juarendra/Zeapad-QMK-VIA/FIRMWARE/zeapadstm32_artsey/keymaps/default/keymap.c

/* Copyright 2024 Juarendra Ramadhani <jrjuarendra@gmail.com>
 *
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
 * You should have received a copy of the GNU General Public License
 * along with this program.  If not, see <http://www.gnu.org/licenses/>.
*/
#include QMK_KEYBOARD_H
#include "midi.h"
//#include "encoder.c"

extern MidiDevice midi_device;


enum layers {
  _ART_BASE,
  _ART_NUM,
  _ART_CUS,
  _ART_PUNC,
  _ART_MOU,
  _ART_NAV,
  _ART_SYM,
};

#include "aliases.c"
#include "combos.c"

#define LAYOUT_via( \
    k00, k01, k02, k03, \
    k10, k11, k12, k13,\
    k20, k21, k22, k23,\
    k30, k31, k32, k33\
) \
{ \
    { k00, k01, k02, k03}, \
    { k10, k11, k12, k13}, \
    { k20, k21, k22, k23}, \
    { k30, k31, k32, k33} \
}

enum midi_cc_keycodes_LTRM { MIDI_CC1 = QK_USER_0, MIDI_CC2, MIDI_CC3, MIDI_CC4, MIDI_CC5, MIDI_CC6, MIDI_CC7, MIDI_CC8, MIDI_CC9, MIDI_CC10, MIDI_CC11, MIDI_CC12, MIDI_CC13, MIDI_CC14, MIDI_CC15, MIDI_ENCH1_1, MIDI_ENCH1_2, MIDI_ENCH2_1, MIDI_ENCH2_2, MIDI_ENCH3_1, MIDI_ENCH3_2};
static uint8_t current_MIDI_ccNumber         = 1;
static uint8_t current_MIDI_ccNumber1        = 16;
static uint8_t current_MIDI_ccNumber2        = 31;


const uint16_t PROGMEM keymaps[][MATRIX_ROWS][MATRIX_COLS] = {

[_ART_BASE] = LAYOUT_via(
    KC_P7,    LCTL(LSFT(KC_E)),             KC_ENTER,                TO(1),    
    KC_P4,    LCTL(KC_C),                   LCTL(KC_V),              KC_ESC,      
	BASE_1_1,		BASE_1_2,		BASE_1_3,		BASE_1_4,
	BASE_2_1,		BASE_2_2,		BASE_2_3,		BASE_2_4
),

[_ART_NUM] = LAYOUT_via(
    KC_TRNS,   KC_TRNS,   KC_TRNS,    TO(2),
    KC_TRNS,   KC_TRNS,   KC_TRNS,    KC_TRNS,
	NUM_1_1,		NUM_1_2,		NUM_1_3,		NUM_1_4,
	NUM_2_1,		NUM_2_2,		NUM_2_3,		NUM_2_4
),

[_ART_CUS] = LAYOUT_via(
    MIDI_CC1,       MIDI_CC2,       MIDI_CC3,       TO(4),   
    MIDI_CC4,       MIDI_CC5,       MIDI_CC6,       MIDI_CC7,  
    CUS_1_1,		CUS_1_2,		CUS_1_3,		CUS_1_4,
	CUS_2_1,		CUS_2_2,		CUS_2_3,		CUS_2_4
),

[_ART_PUNC] = LAYOUT_via(
    KC_TRNS,   KC_TRNS,   KC_TRNS,    TO(3),
    KC_TRNS,   KC_TRNS,   KC_TRNS,    KC_TRNS,
	PUNC_1_1 ,		PUNC_1_2,		PUNC_1_3,		PUNC_1_4,
	PUNC_2_1,		PUNC_2_2,		PUNC_2_3,		PUNC_2_4
),

[_ART_MOU] = LAYOUT_via(
    MIDI_CC1,       MIDI_CC2,       MIDI_CC3,       TO(6),   
    MIDI_CC4,       MIDI_CC5,       MIDI_CC6,       MIDI_CC7,  
	MOU_1_1,		MOU_1_2,		MOU_1_3,		MOU_1_4,
	MOU_2_1,		MOU_2_2,		MOU_2_3,		MOU_2_4
),

[_ART_NAV] = LAYOUT_via(
    MIDI_CC1,       MIDI_CC2,       MIDI_CC3,       TO(0),   
    MIDI_CC4,       MIDI_CC5,       MIDI_CC6,       MIDI_CC7,  
	NAV_1_1,		NAV_1_2,		NAV_1_3,		NAV_1_4,
	NAV_2_1,		NAV_2_2,		NAV_2_3,		NAV_2_4
),

[_ART_SYM] = LAYOUT_via(
    MIDI_CC1,       MIDI_CC2,       MIDI_CC3,       TO(5),   
    MIDI_CC4,       MIDI_CC5,       MIDI_CC6,       MIDI_CC7,  
	SYM_1_1,		SYM_1_2,		SYM_1_3,		SYM_1_4,
	SYM_2_1,		SYM_2_2,		SYM_2_3,		SYM_2_4
)
};


bool process_record_user(uint16_t keycode, keyrecord_t *record) {
	#ifdef CONSOLE_ENABLE
    uprintf("KL: kc: 0x%04X, col: %u, row: %u, pressed: %b, time: %u, interrupt: %b, count: %u\n", keycode, record->event.key.col, record->event.key.row, record->event.pressed, record->event.time, record->tap.interrupted, record->tap.count);
	#endif
    switch (keycode) {
        case MIDI_CC1:
            if (record->event.pressed) {
                current_MIDI_ccNumber         = 1;
                current_MIDI_ccNumber1        = 16;
                current_MIDI_ccNumber2        = 31;
            } else {
            }
            return false;
            break;
        case MIDI_CC2:
            if (record->event.pressed) {
                current_MIDI_ccNumber         = 2;
                current_MIDI_ccNumber1        = 17;
                current_MIDI_ccNumber2        = 32;
            } else {
            }
            return false;
            break;
        case MIDI_CC3:
            if (record->event.pressed) {
                current_MIDI_ccNumber         = 3;
                current_MIDI_ccNumber1        = 18;
                current_MIDI_ccNumber2        = 33;
            } else {
            }
            return false;
            break;
        case MIDI_CC4:
            if (record->event.pressed) {
                current_MIDI_ccNumber         = 4;
                current_MIDI_ccNumber1        = 19;
                current_MIDI_ccNumber2        = 34;
            } else {
            }
            return false;
            break;
        case MIDI_CC5:
            if (record->event.pressed) {
                current_MIDI_ccNumber         = 5;
                current_MIDI_ccNumber1        = 20;
                current_MIDI_ccNumber2        = 35;
            } else {
            }
            return false;
            break;
        case MIDI_CC6:
            if (record->event.pressed) {
                current_MIDI_ccNumber         = 6;
                current_MIDI_ccNumber1        = 21;
                current_MIDI_ccNumber2        = 36;
            } else {
            }
            return false;
            break;
        case MIDI_CC7:
            if (record->event.pressed) {
                current_MIDI_ccNumber         = 7;
                current_MIDI_ccNumber1        = 22;
                current_MIDI_ccNumber2        = 37;
            } else {
            }
            return false;
            break;
        case MIDI_CC8:
            if (record->event.pressed) {
                current_MIDI_ccNumber         = 8;
                current_MIDI_ccNumber1        = 23;
                current_MIDI_ccNumber2        = 38;
            } else {
            }
            return false;
            break;
        case MIDI_CC9:
            if (record->event.pressed) {
                current_MIDI_ccNumber         = 9;
                current_MIDI_ccNumber1        = 24;
                current_MIDI_ccNumber2        = 39;
            } else {
            }
            return false;
            break;
        case MIDI_CC10:
            if (record->event.pressed) {
                current_MIDI_ccNumber         = 10;
                current_MIDI_ccNumber1        = 25;
                current_MIDI_ccNumber2        = 40;
            } else {
            }
            return false;
            break;
        case MIDI_CC11:
            if (record->event.pressed) {
                current_MIDI_ccNumber         = 11;
                current_MIDI_ccNumber1        = 26;
                current_MIDI_ccNumber2        = 41;
            } else {
            }
            return false;
            break;
        case MIDI_CC12:
            if (record->event.pressed) {
                current_MIDI_ccNumber         = 12;
                current_MIDI_ccNumber1        = 27;
                current_MIDI_ccNumber2        = 42;
            } else {
            }
            return false;
            break;
        case MIDI_CC13:
            if (record->event.pressed) {
                current_MIDI_ccNumber         = 13;
                current_MIDI_ccNumber1        = 28;
                current_MIDI_ccNumber2        = 43;
            } else {
            }
            return false;
            break;
        case MIDI_CC14:
            if (record->event.pressed) {
                current_MIDI_ccNumber         = 14;
                current_MIDI_ccNumber1        = 29;
                current_MIDI_ccNumber2        = 44;
            } else {
            }
            return false;
            break;
        case MIDI_CC15:
            if (record->event.pressed) {
                current_MIDI_ccNumber         = 15;
                current_MIDI_ccNumber1        = 30;
                current_MIDI_ccNumber2        = 45;
            } else {
            }
            return false;
            break;
        case MIDI_ENCH1_1:
            if (record->event.pressed) {
                midi_send_cc(&midi_device, 0, current_MIDI_ccNumber, 65);
            } else {
            }
            return true;
        case MIDI_ENCH1_2:
            if (record->event.pressed) {
                midi_send_cc(&midi_device, 0, current_MIDI_ccNumber, 63);
            } else {
            }
            return true;
        case MIDI_ENCH2_1:
            if (record->event.pressed) {
                midi_send_cc(&midi_device, 0, current_MIDI_ccNumber1, 65);
            } else {
            }
            return true;
        case MIDI_ENCH2_2:
            if (record->event.pressed) {
                midi_send_cc(&midi_device, 0, current_MIDI_ccNumber1, 63);
            } else {
            }
            return true;
        case MIDI_ENCH3_1:
            if (record->event.pressed) {
                midi_send_cc(&midi_device, 0, current_MIDI_ccNumber2, 65);
            } else {
            }
            return true;
        case MIDI_ENCH3_2:
            if (record->event.pressed) {
                midi_send_cc(&midi_device, 0, current_MIDI_ccNumber2, 63);
            } else {
            }
            return true;
        default:
            break;
    }
    return true;
}


#if defined(ENCODER_MAP_ENABLE)
const uint16_t PROGMEM encoder_map[][NUM_ENCODERS][NUM_DIRECTIONS] = {
    [_ART_BASE] = { ENCODER_CCW_CW(KC_VOLU, KC_VOLD), ENCODER_CCW_CW(KC_PGUP, KC_PGDN) },
    [_ART_NUM] = { ENCODER_CCW_CW(KC_TRNS, KC_TRNS), ENCODER_CCW_CW(KC_TRNS, KC_TRNS) },
    [_ART_PUNC] = { ENCODER_CCW_CW(KC_TRNS, KC_TRNS), ENCODER_CCW_CW(KC_TRNS, KC_TRNS) },
    [_ART_CUS] = { ENCODER_CCW_CW(KC_TRNS, KC_TRNS), ENCODER_CCW_CW(KC_TRNS, KC_TRNS) },
    [_ART_SYM] = { ENCODER_CCW_CW(KC_TRNS, KC_TRNS), ENCODER_CCW_CW(KC_TRNS, KC_TRNS) },
    [_ART_MOU] = { ENCODER_CCW_CW(KC_TRNS, KC_TRNS), ENCODER_CCW_CW(KC_TRNS, KC_TRNS) },
    [_ART_NAV] = { ENCODER_CCW_CW(KC_TRNS, KC_TRNS), ENCODER_CCW_CW(KC_TRNS, KC_TRNS) }
};
#endif

/*
void keyboard_post_init_user(void) {
    rgblight_sethsv(128, 255, 120);
}

layer_state_t layer_state_set_user(layer_state_t state) {
    switch (get_highest_layer(state)) {
        case _FN1:
            rgblight_sethsv(43, 255, 120);
            break;
        case _FN2:
            rgblight_sethsv(85, 255, 120);
            break;
        case _FN3:
            rgblight_sethsv(191, 255, 120);
            break;
        case _BASE:
            rgblight_sethsv(128, 255, 120);
            break;
        default: // for any other layers, or the default layer
            rgblight_sethsv(128, 255, 120);
            break;
    }
  return state;
}
 */
